SuperFola/floppy/pcbs/keyboard/floppy.kicad_sch

## KiCad design pcbs/keyboard/floppy.kicad_sch (2024-10-25)

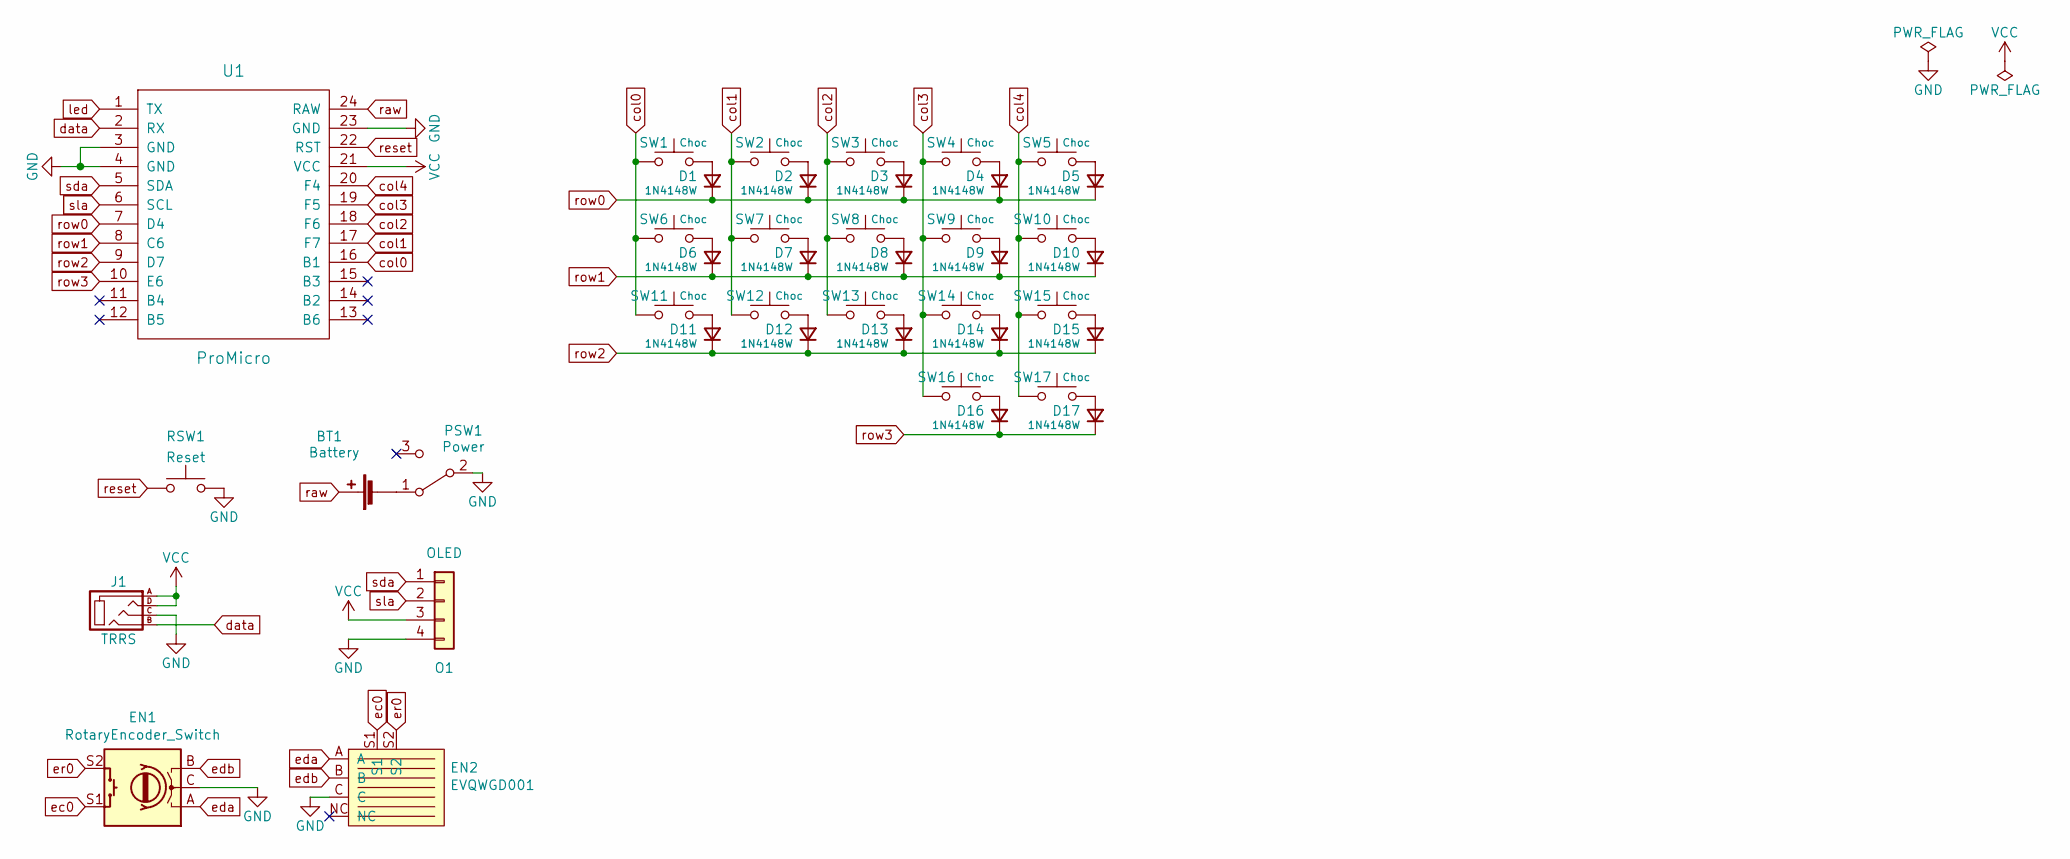
[picture p3: schematic floppy.kicad_sch]

Parts:
BT1: Battery; Battery_pads
D1, D2, D3, D4, D5, D6, D7, D8, D9, D10, D11, D12, D13, D14, D15, D16, D17: 1N4148W; D3_SMD
EN1: RotaryEncoder_Switch; RotaryEncoder
EN2: EVQWGD001; RollerEncoder
J1: TRRS; TRRS-3pin
O1: OLED; OLED_jumpers
PSW1: Power
RSW1: Reset
SW1, SW2, SW3, SW4, SW5, SW6, SW7, SW8, SW9, SW10, SW11, SW12, SW13, SW14, SW15, SW16, SW17: Choc
U1: ProMicro; ProMicro_jumpers

Connections:
GND: EN1.C, EN2.C, J1.C, O1.4, PSW1.2 (B), RSW1.2, U1.3 (GND), U1.4 (GND), U1.23 (GND)
unnamed: BT1.2 (-), PSW1.1 (A)
unnamed: D1.2 (A), SW1.2
unnamed: D2.2 (A), SW2.2
unnamed: D3.2 (A), SW3.2
unnamed: D4.2 (A), SW4.2
unnamed: D5.2 (A), SW5.2
unnamed: D6.2 (A), SW6.2
unnamed: D7.2 (A), SW7.2
unnamed: D8.2 (A), SW8.2
unnamed: D9.2 (A), SW9.2
unnamed: D10.2 (A), SW10.2
unnamed: D11.2 (A), SW11.2
unnamed: D12.2 (A), SW12.2
unnamed: D13.2 (A), SW13.2
unnamed: D14.2 (A), SW14.2
unnamed: D15.2 (A), SW15.2
unnamed: D16.2 (A), SW16.2
unnamed: D17.2 (A), SW17.2
VCC: J1.A, J1.D, O1.3, U1.21 (VCC)
col0: SW1.1, SW6.1, SW11.1, U1.16 (B1)
col1: SW2.1, SW7.1, SW12.1, U1.17 (F7)
col2: SW3.1, SW8.1, SW13.1, U1.18 (F6)
col3: SW4.1, SW9.1, SW14.1, SW16.1, U1.19 (F5)
col4: SW5.1, SW10.1, SW15.1, SW17.1, U1.20 (F4)
data: J1.B, U1.2 (RX)
ec0: EN1.S1, EN2.S1
eda: EN1.A, EN2.A
edb: EN1.B, EN2.B
er0: EN1.S2, EN2.S2
led: U1.1 (TX)
raw: BT1.1 (+), U1.24 (RAW)
reset: RSW1.1, U1.22 (RST)
row0: D1.1 (K), D2.1 (K), D3.1 (K), D4.1 (K), D5.1 (K), U1.7 (D4)
row1: D6.1 (K), D7.1 (K), D8.1 (K), D9.1 (K), D10.1 (K), U1.8 (C6)
row2: D11.1 (K), D12.1 (K), D13.1 (K), D14.1 (K), D15.1 (K), U1.9 (D7)
row3: D16.1 (K), D17.1 (K), U1.10 (E6)
sda: O1.1, U1.5 (SDA)
sla: O1.2, U1.6 (SCL)
